samuel235/Homini-Pulse-Meter-Monitor/controller/images/1.png

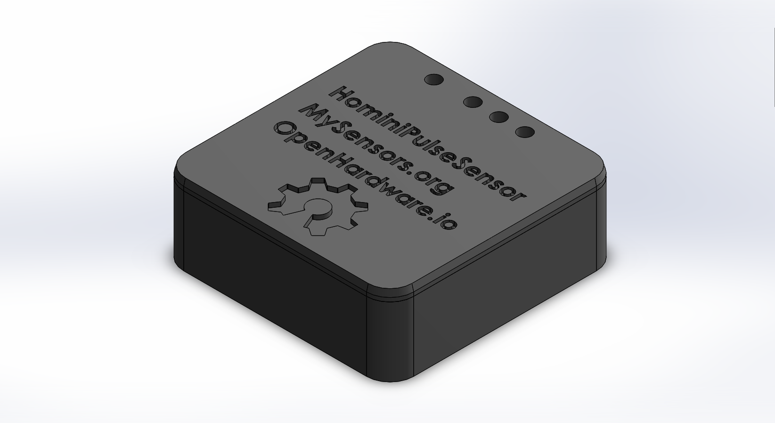
controller/images/1.png
