samuel235/Homini-Pulse-Meter-Monitor/controller/images/2.png

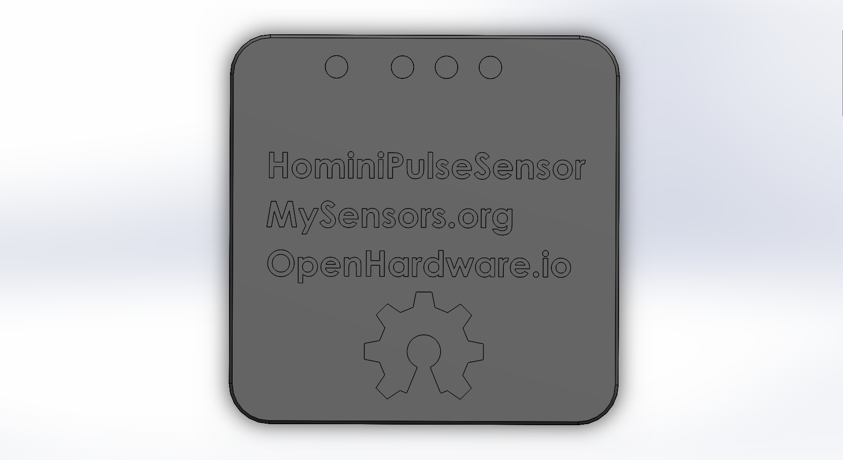
controller/images/2.png
