samuel235/Homini-Pulse-Meter-Monitor/controller/images/3.png

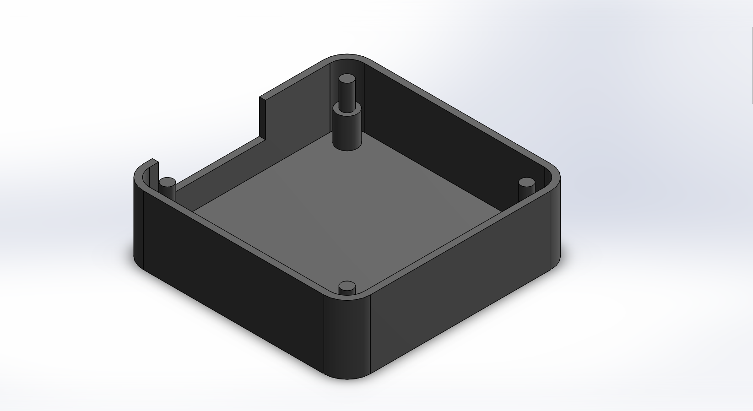
controller/images/3.png
