samuel235/Homini-Pulse-Meter-Monitor/controller/images/controller_PCB.jpg

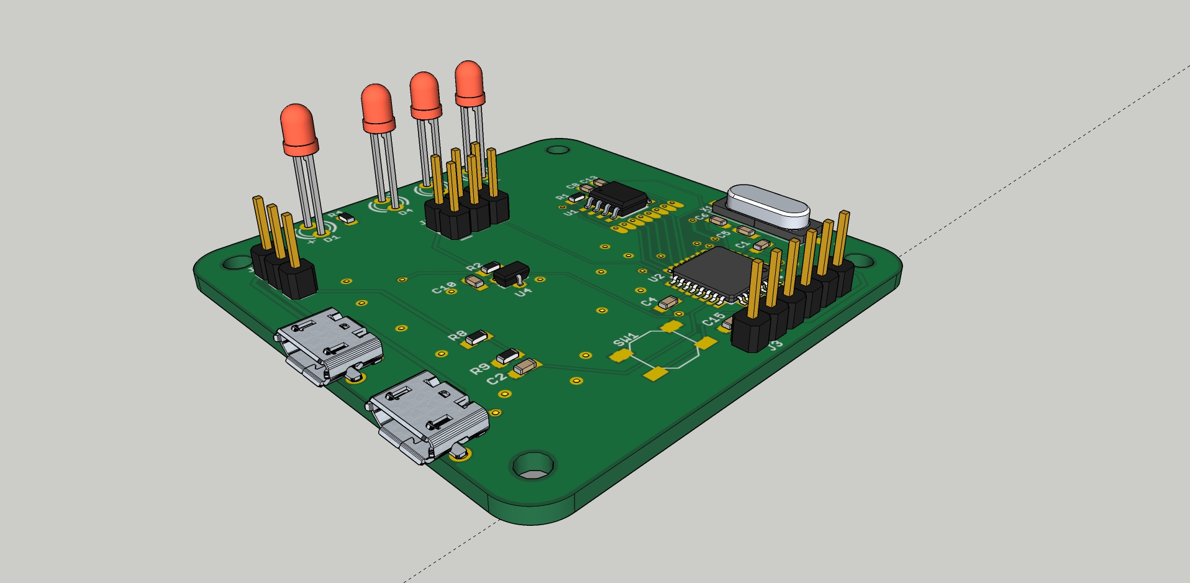
controller/images/controller_PCB.jpg
