samuel235/Homini-Pulse-Meter-Monitor/controller/images/controller_PCB_2.jpg

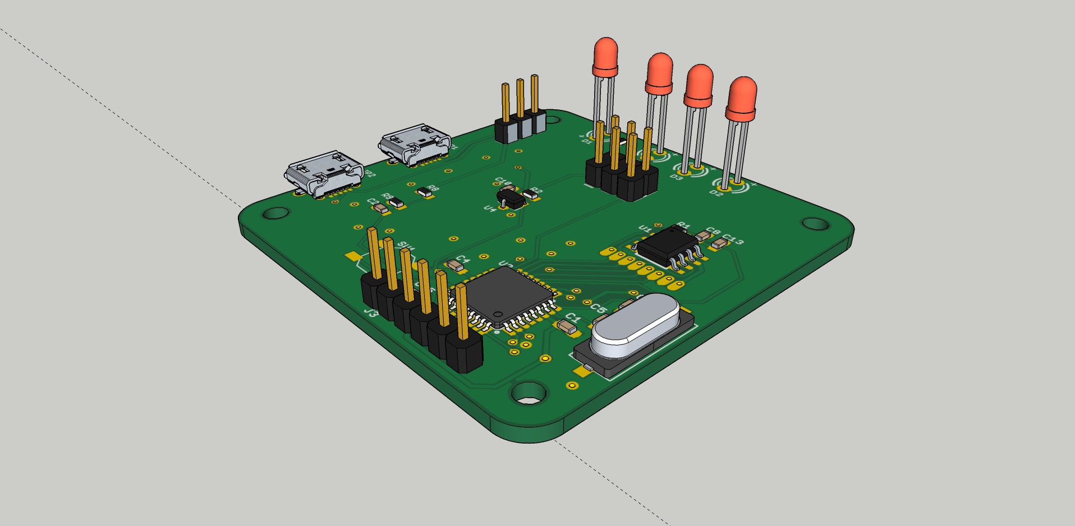
controller/images/controller_PCB_2.jpg
