samuel235/Homini-Pulse-Meter-Monitor/controller/images/controller_PCB_4.jpg

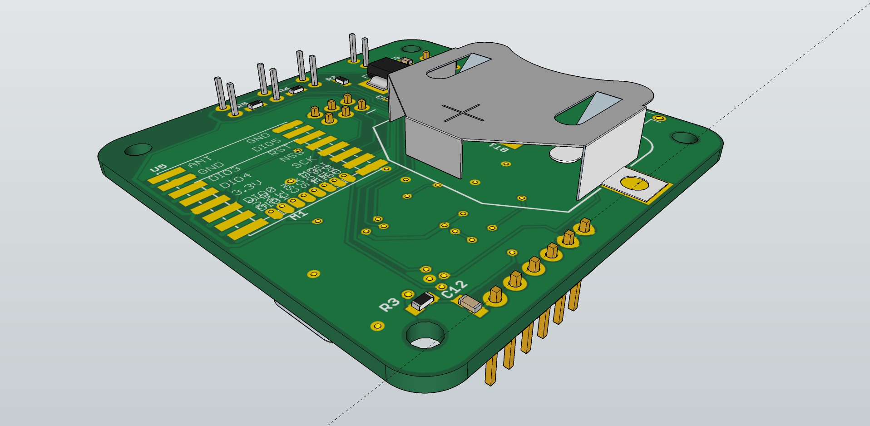
controller/images/controller_PCB_4.jpg
