samuel235/Homini-Pulse-Meter-Monitor/sensor/images/2.jpeg

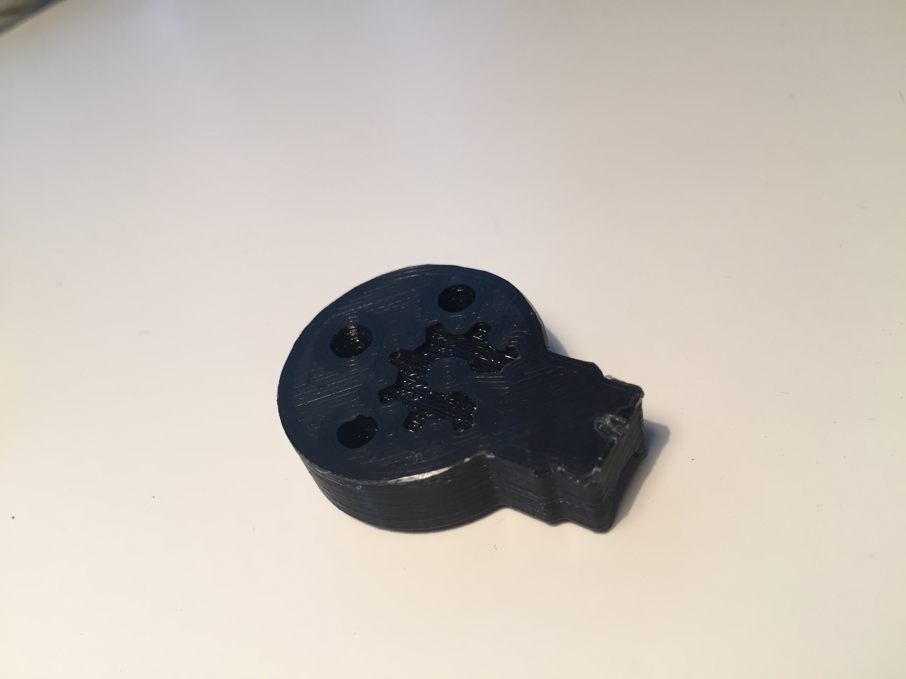
sensor/images/2.jpeg
