samuel235/Homini-Pulse-Meter-Monitor/sensor/images/4.jpeg

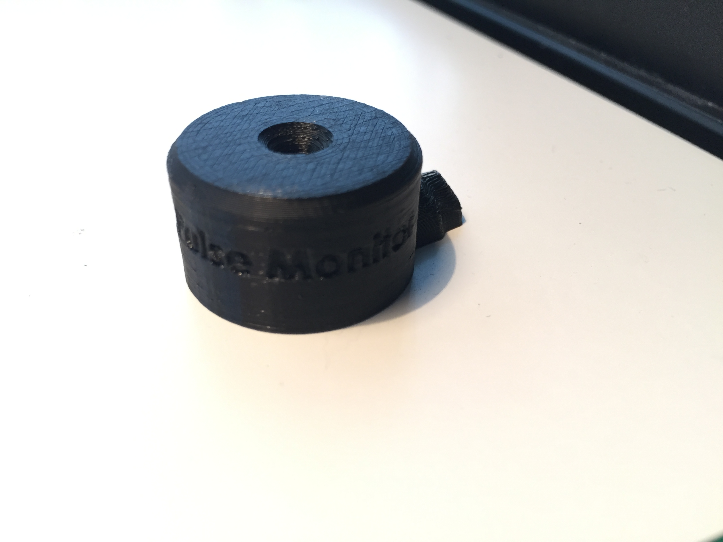
sensor/images/4.jpeg
