samuel235/Homini-Pulse-Meter-Monitor/sensor/images/View2.JPG

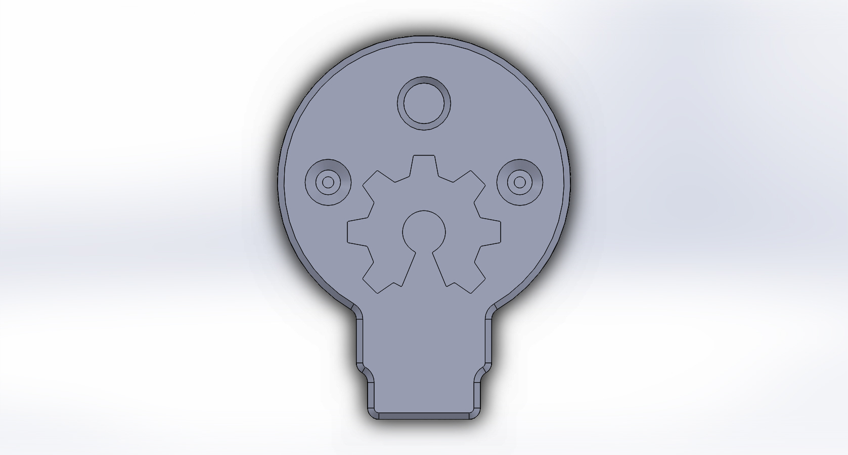
sensor/images/View2.JPG
