samuel235/Homini-Pulse-Meter-Monitor/sensor/images/View4.JPG

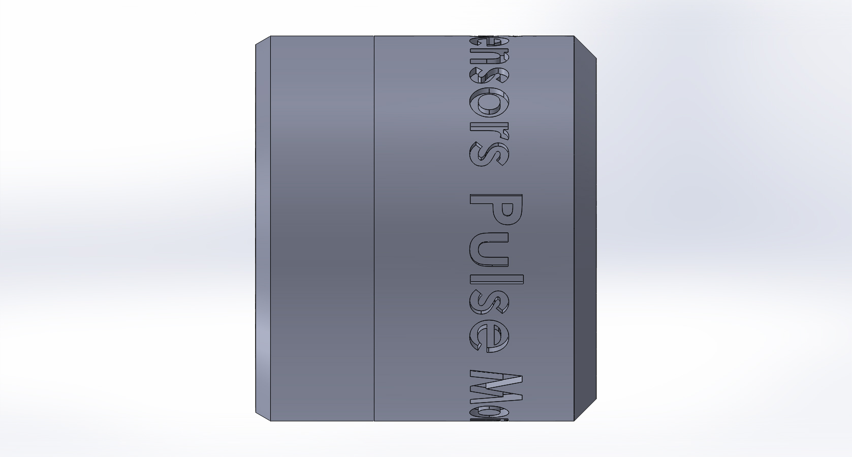
sensor/images/View4.JPG
