samuel235/Homini-Pulse-Meter-Monitor/sensor/images/View5.JPG

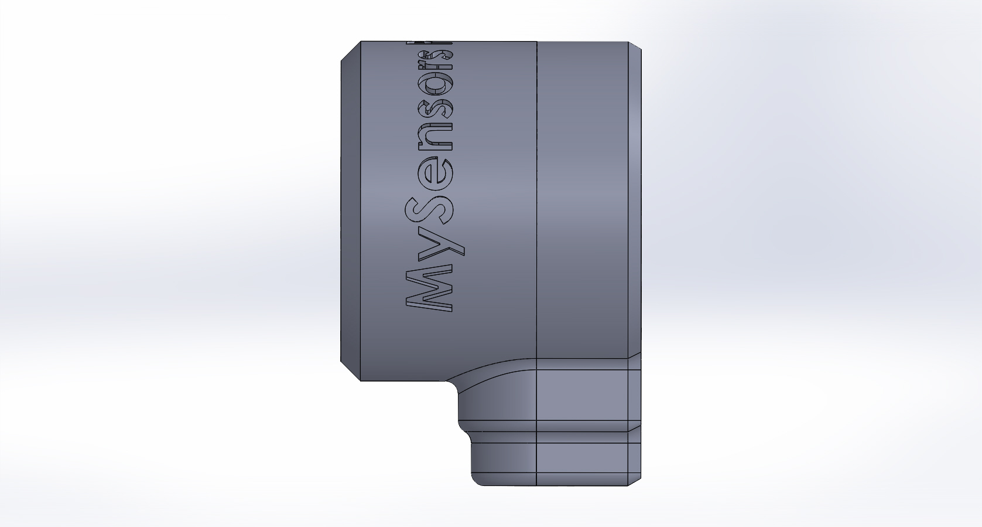
sensor/images/View5.JPG
