samuel235/Homini-Pulse-Meter-Monitor/sensor/images/View6.JPG

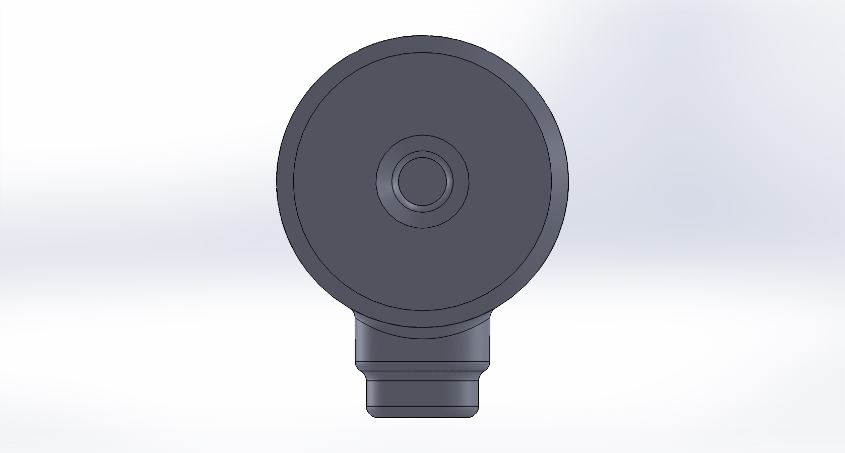
sensor/images/View6.JPG
