samuel235/Homini-Pulse-Meter-Monitor/sensor/images/View7.JPG

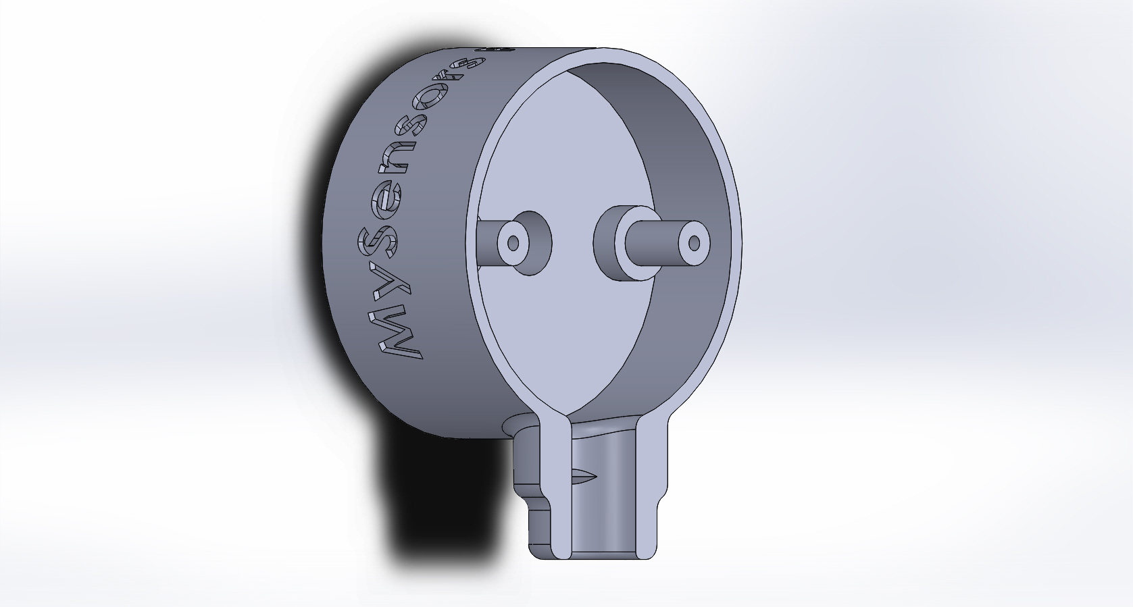
sensor/images/View7.JPG
