samuel235/Homini-Pulse-Meter-Monitor/sensorbatt/images/SensorBatt_PCB.jpg

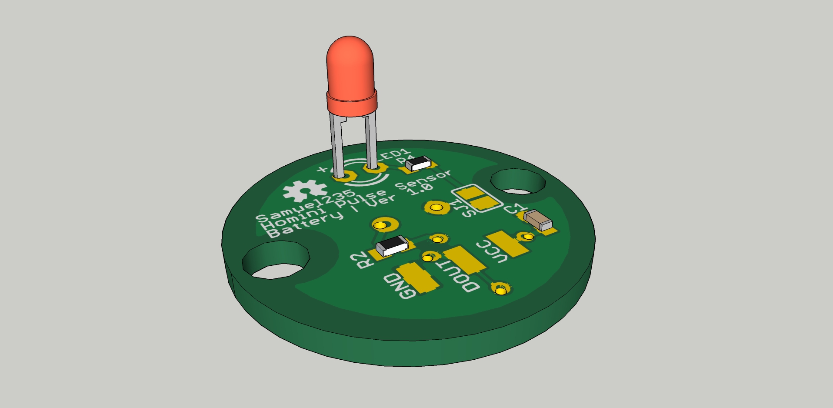
sensorbatt/images/SensorBatt_PCB.jpg
