samuel235/Homini-Pulse-Meter-Monitor/sensorbatt/images/SensorBatt_PCB_2.jpg

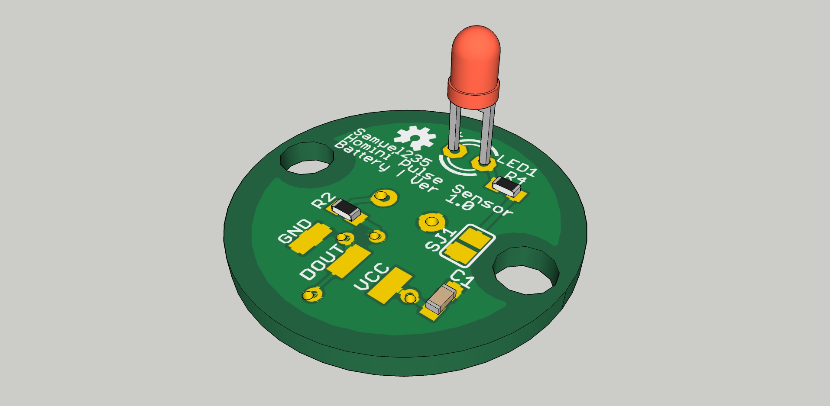
sensorbatt/images/SensorBatt_PCB_2.jpg
